robinhedwards/A8PicoCart/source/Pico VSCode Project/a8_pico_cart/osrom.h

unsigned const char os_rom[] = {
  0x00, 0x00, 0x01, 0x01, 0x13, 0x02, 0x43, 0x58, 0x00, 0x00, 0x00, 0x00,
  0x2d, 0xff, 0xd1, 0xf0, 0x4d, 0x8d, 0x8c, 0x02, 0x8a, 0x48, 0xad, 0x8c,
  0x02, 0x6c, 0x38, 0x02, 0xa9, 0xef, 0x20, 0xb8, 0xc0, 0x6c, 0x0c, 0x02,
  0x2c, 0x0e, 0xd2, 0xd0, 0x41, 0x6c, 0x0e, 0x02, 0xa9, 0xfe, 0x20, 0xb8,
  0xc0, 0x6c, 0x10, 0x02, 0xa9, 0xfd, 0x20, 0xb8, 0xc0, 0x6c, 0x12, 0x02,
  0xa9, 0xfb, 0x20, 0xb8, 0xc0, 0x6c, 0x14, 0x02, 0x48, 0xa9, 0x20, 0x2c,
  0x0e, 0xd2, 0xd0, 0x0d, 0xa9, 0xdf, 0x8d, 0x0e, 0xd2, 0xa5, 0x10, 0x8d,
  0x0e, 0xd2, 0x6c, 0x0a, 0x02, 0xad, 0x49, 0x02, 0xd0, 0xae, 0xa9, 0x10,
  0x2c, 0x0e, 0xd2, 0xf0, 0xb7, 0x4a, 0x24, 0x10, 0xd0, 0xba, 0xad, 0x0e,
  0xd2, 0x4a, 0x90, 0xbc, 0x4a, 0x90, 0xc1, 0x4a, 0x90, 0xc6, 0x2c, 0x0e,
  0xd2, 0x50, 0x21, 0x10, 0x27, 0x2c, 0x02, 0xd3, 0x30, 0x2a, 0x2c, 0x03,
  0xd3, 0x30, 0x2b, 0x68, 0x8d, 0x8c, 0x02, 0x68, 0x48, 0x29, 0x10, 0xf0,
  0x07, 0xad, 0x8c, 0x02, 0x48, 0x6c, 0x06, 0x02, 0xad, 0x8c, 0x02, 0x40,
  0xa9, 0xbf, 0x20, 0xb8, 0xc0, 0x6c, 0x08, 0x02, 0xa9, 0x7f, 0x20, 0xb8,
  0xc0, 0x6c, 0x36, 0x02, 0xad, 0x00, 0xd3, 0x6c, 0x02, 0x02, 0xad, 0x01,
  0xd3, 0x6c, 0x04, 0x02, 0x8d, 0x0e, 0xd2, 0xa5, 0x10, 0x8d, 0x0e, 0xd2,
  0x60, 0xff, 0xff, 0xff, 0xff, 0xff, 0xff, 0xff, 0xff, 0xff, 0xff, 0xff,
  0xff, 0xff, 0xff, 0xff, 0xff, 0xff, 0xff, 0xff, 0xff, 0xff, 0xff, 0xff,
  0xff, 0xff, 0xff, 0xff, 0xff, 0xff, 0xff, 0xff, 0xff, 0xff, 0xe6, 0x14,
  0xd0, 0x08, 0xe6, 0x4d, 0xe6, 0x13, 0xd0, 0x02, 0xe6, 0x12, 0xa2, 0xfe,
  0xa9, 0x00, 0xa4, 0x4d, 0x10, 0x06, 0x86, 0x4d, 0xa2, 0xf6, 0xa5, 0x13,
  0x86, 0x4e, 0x85, 0x4f, 0x4d, 0xc5, 0x02, 0x25, 0x4e, 0x8d, 0x17, 0xd0,
  0xad, 0x18, 0x02, 0xd0, 0x0d, 0xad, 0x19, 0x02, 0xf0, 0x15, 0xce, 0x19,
  0x02, 0xce, 0x18, 0x02, 0xd0, 0x0d, 0xce, 0x18, 0x02, 0xd0, 0x08, 0xad,
  0x19, 0x02, 0xd0, 0x03, 0x20, 0x31, 0xc1, 0xa5, 0x42, 0xf0, 0x09, 0x68,
  0xa8, 0x68, 0xaa, 0x68, 0x40, 0x6c, 0x26, 0x02, 0xa9, 0x04, 0xba, 0x3d,
  0x04, 0x01, 0xd0, 0xef, 0x58, 0xad, 0x31, 0x02, 0x8d, 0x03, 0xd4, 0xad,
  0x30, 0x02, 0x8d, 0x02, 0xd4, 0xad, 0x2f, 0x02, 0x8d, 0x00, 0xd4, 0xad,
  0xf4, 0x02, 0x8d, 0x09, 0xd4, 0xad, 0xf3, 0x02, 0x8d, 0x01, 0xd4, 0xad,
  0x6f, 0x02, 0x8d, 0x1b, 0xd0, 0xa2, 0x08, 0x8e, 0x1f, 0xd0, 0xbd, 0xc0,
  0x02, 0x45, 0x4f, 0x25, 0x4e, 0x9d, 0x12, 0xd0, 0xca, 0x10, 0xf3, 0xa2,
  0x03, 0x20, 0x22, 0xc2, 0xd0, 0x03, 0x20, 0x1f, 0xc2, 0xa2, 0x09, 0x18,
  0x20, 0x22, 0xc2, 0xb0, 0x07, 0xf0, 0x02, 0xa9, 0xff, 0x9d, 0x25, 0x02,
  0xca, 0xca, 0xe0, 0x05, 0xb0, 0xed, 0xad, 0x0f, 0xd2, 0x29, 0x04, 0xd0,
  0x13, 0xce, 0x2b, 0x02, 0xd0, 0x13, 0xad, 0x09, 0xd2, 0x8d, 0xfc, 0x02,
  0xad, 0xda, 0x02, 0x8d, 0x2b, 0x02, 0xd0, 0x0d, 0xa9, 0x00, 0x8d, 0x2b,
  0x02, 0xad, 0xf1, 0x02, 0xf0, 0x03, 0xce, 0xf1, 0x02, 0xad, 0x00, 0xd3,
  0xaa, 0x29, 0x0f, 0x8d, 0x78, 0x02, 0x8d, 0x7a, 0x02, 0x8a, 0x4a, 0x4a,
  0xaa, 0x4a, 0x4a, 0x8d, 0x79, 0x02, 0x8d, 0x7b, 0x02, 0x4a, 0x4a, 0xa8,
  0x29, 0x01, 0x8d, 0x7e, 0x02, 0x98, 0x4a, 0x8d, 0x7f, 0x02, 0x8a, 0x29,
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
};
unsigned int os_rom_len = 16384;
