robinhedwards/A8PicoCart/source/Pico VSCode Project/a8_pico_cart/rom.h

unsigned char A8PicoCart_rom[] = {
  0x60, 0xad, 0x14, 0xd0, 0xc9, 0x01, 0xf0, 0x0d, 0xa9, 0x6f, 0x8d, 0xc5,
  0x02, 0xa9, 0x62, 0x8d, 0xc6, 0x02, 0x4c, 0x1f, 0xa0, 0xa9, 0x4f, 0x8d,
  0xc5, 0x02, 0xa9, 0x42, 0x8d, 0xc6, 0x02, 0xa9, 0x03, 0x85, 0x09, 0xa9,
  0x05, 0x85, 0x02, 0xa9, 0xa3, 0x85, 0x03, 0x20, 0x27, 0xa5, 0x20, 0xf5,
  0xa6, 0x20, 0x0c, 0xa7, 0x20, 0x64, 0xa4, 0x20, 0xad, 0xa1, 0xad, 0x10,
  0xd0, 0xd0, 0x03, 0x20, 0x66, 0xa3, 0xa9, 0x00, 0x85, 0x87, 0xa9, 0x01,
  0x20, 0x20, 0x06, 0xad, 0x01, 0xd5, 0xc9, 0x01, 0xd0, 0x06, 0x20, 0x0f,
  0xa3, 0x4c, 0x42, 0xa0, 0xad, 0x02, 0xd5, 0x85, 0x80, 0xa9, 0x00, 0x85,
  0x84, 0xa9, 0x00, 0x85, 0x85, 0x20, 0x96, 0xa5, 0x20, 0x0f, 0xa4, 0xa5,
  0x80, 0xd0, 0x09, 0x20, 0xc1, 0xa5, 0x20, 0xdd, 0xa4, 0x4c, 0x7e, 0xa0,
  0x20, 0xb2, 0xa3, 0x20, 0x44, 0xa4, 0x20, 0xf3, 0xa1, 0x20, 0x52, 0xa4,
  0xf0, 0x33, 0xc9, 0x1c, 0xf0, 0x6c, 0xc9, 0x2d, 0xf0, 0x68, 0xc9, 0x1d,
  0xf0, 0x3f, 0xc9, 0x3d, 0xf0, 0x3b, 0xc9, 0x62, 0xd0, 0x03, 0x4c, 0x4a,
  0xa1, 0xc9, 0x1e, 0xd0, 0x03, 0x4c, 0x4a, 0xa1, 0xc9, 0x9b, 0xd0, 0x03,
  0x4c, 0x14, 0xa1, 0xc9, 0x78, 0xd0, 0x03, 0x4c, 0x58, 0xa1, 0xc9, 0x1b,
  0xd0, 0x03, 0x4c, 0x79, 0xa1, 0x20, 0xba, 0xa1, 0xa5, 0x8b, 0xc9, 0x01,
  0xf0, 0x52, 0xa5, 0x8c, 0x29, 0x01, 0xd0, 0x2e, 0xa5, 0x8c, 0x29, 0x02,
  0xd0, 0x03, 0x4c, 0x7e, 0xa0, 0xa5, 0x85, 0x18, 0x69, 0x01, 0xc5, 0x80,
  0xb0, 0xa4, 0xe6, 0x85, 0xa5, 0x85, 0x38, 0xe5, 0x84, 0x18, 0xc9, 0x0f,
  0xf0, 0x06, 0x20, 0x44, 0xa4, 0x4c, 0x7e, 0xa0, 0xa5, 0x84, 0x18, 0x69,
  0x0f, 0x85, 0x84, 0x4c, 0x65, 0xa0, 0xa5, 0x85, 0xc9, 0x00, 0xf0, 0x82,
  0xc6, 0x85, 0xa5, 0x85, 0xc5, 0x84, 0x30, 0x06, 0x20, 0x44, 0xa4, 0x4c,
  0x7e, 0xa0, 0xa5, 0x84, 0x38, 0xe9, 0x0f, 0x85, 0x84, 0x4c, 0x65, 0xa0,
  0xa5, 0x80, 0xd0, 0x03, 0x4c, 0x7e, 0xa0, 0xa5, 0x85, 0x8d, 0x00, 0xd5,
  0xa9, 0x00, 0x20, 0x20, 0x06, 0xad, 0x01, 0xd5, 0xc9, 0x00, 0xf0, 0x12,
  0xc9, 0x01, 0xf0, 0x11, 0xc9, 0x02, 0xf0, 0x10, 0xc9, 0x03, 0xf0, 0x0f,
  0x20, 0x0f, 0xa3, 0x4c, 0x42, 0xa0, 0x4c, 0x42, 0xa0, 0x4c, 0x30, 0x06,
  0x4c, 0x60, 0xa1, 0x4c, 0x69, 0xa1, 0xa5, 0x87, 0xc9, 0x01, 0xf0, 0x05,
  0xa9, 0x03, 0x20, 0x20, 0x06, 0x4c, 0x42, 0xa0, 0xa9, 0xfe, 0x20, 0x20,
  0x06, 0x4c, 0x30, 0x06, 0x20, 0xb0, 0xa4, 0x20, 0x21, 0xa7, 0x4c, 0x03,
  0x07, 0x20, 0xb0, 0xa4, 0x20, 0xfe, 0xa1, 0xc9, 0x00, 0xf0, 0x03, 0x4c,
  0x42, 0xa0, 0x4c, 0x30, 0x06, 0x20, 0xf1, 0xa5, 0x20, 0x8b, 0xa2, 0xa5,
  0x86, 0xc9, 0x00, 0xd0, 0x03, 0x4c, 0x65, 0xa0, 0xa0, 0x00, 0xb9, 0x00,
  0x06, 0x99, 0x00, 0xd5, 0xc8, 0x98, 0xc5, 0x86, 0x90, 0xf4, 0xa9, 0x00,
  0x99, 0x00, 0xd5, 0x20, 0x0f, 0xa4, 0x20, 0xd9, 0xa5, 0xa9, 0x05, 0x20,
  0x20, 0x06, 0xa9, 0x01, 0x85, 0x87, 0x4c, 0x4b, 0xa0, 0xa9, 0x01, 0x85,
  0x88, 0xa9, 0x0f, 0x85, 0x89, 0xa9, 0x00, 0x85, 0x8a, 0x60, 0xa9, 0x00,
  0x85, 0x8b, 0xa9, 0x00, 0x85, 0x8c, 0xa5, 0x8a, 0xf0, 0x02, 0xc6, 0x8a,
  0xad, 0x10, 0xd0, 0xc5, 0x88, 0xd0, 0x19, 0xad, 0x78, 0x02, 0x29, 0x0f,
  0xc5, 0x89, 0xd0, 0x05, 0xa4, 0x8a, 0xf0, 0x01, 0x60, 0x85, 0x89, 0x49,
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
};
unsigned int A8PicoCart_rom_len = 8192;
